SouthwestAir/SWABadge-BLE/01-BLE-circuit/circuit/02-04-seeed_pins_used.png

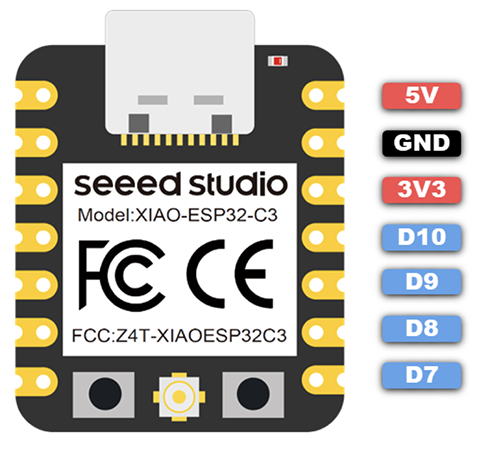
01-BLE-circuit/circuit/02-04-seeed_pins_used.png
