SouthwestAir/SWABadge-BLE/01-BLE-circuit/circuit/circuit01.jpg

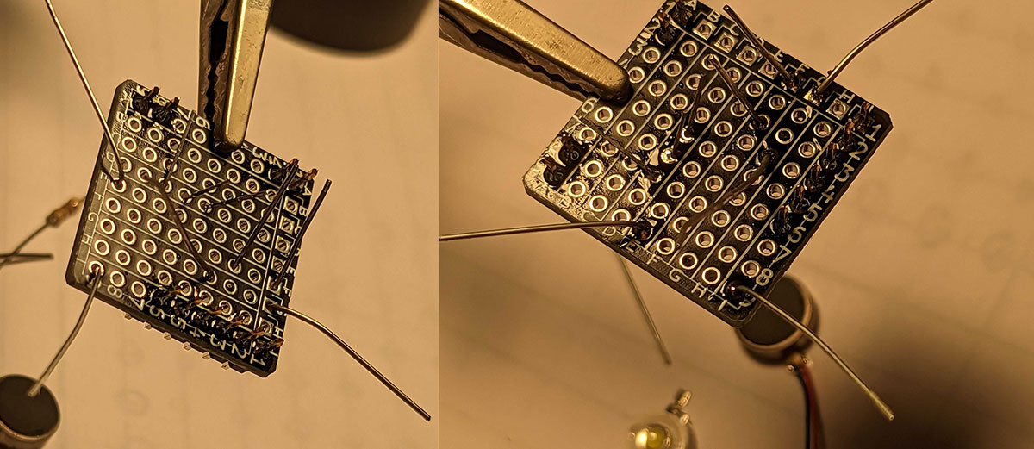
01-BLE-circuit/circuit/circuit01.jpg
