SouthwestAir/SWABadge-BLE/01-BLE-circuit/circuit/circuit03.jpg

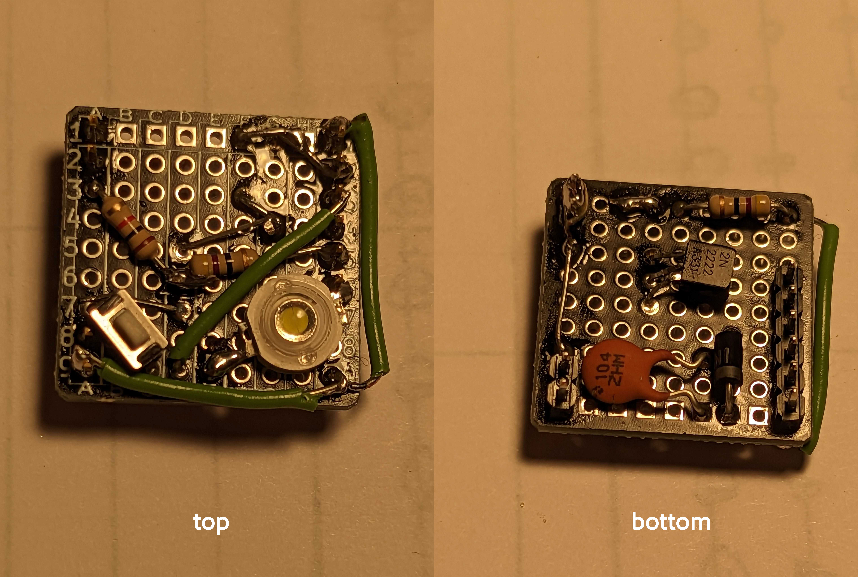
01-BLE-circuit/circuit/circuit03.jpg
