SouthwestAir/SWABadge-BLE/screenshots/02-04-seeed.png

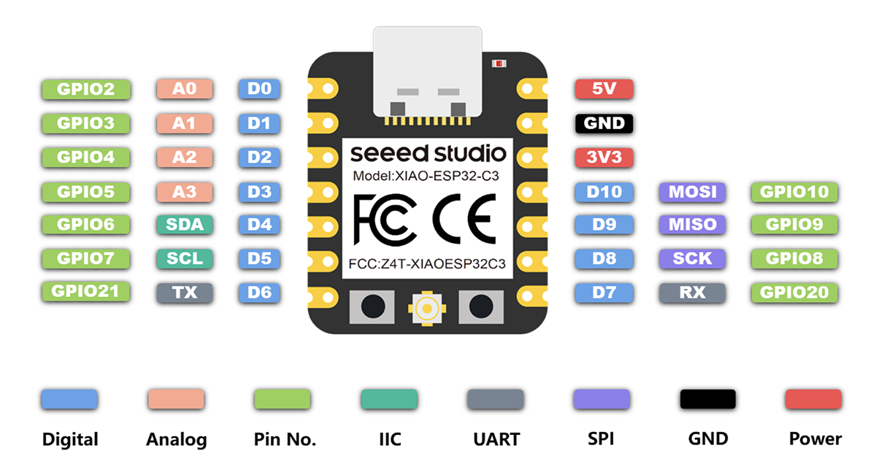
screenshots/02-04-seeed.png
